charliexp/radmatrix/firmware/src/leds.cpp

#include <Arduino.h>
#include "hardware/gpio.h"
#include "pico/multicore.h"
#include "hardware/pio.h"

#include "leds.h"
#include "leds.pio.h"

PIO leds_pio = pio0;
uint pusher_sm = 255; // invalid
uint delay_sm = 255; // invalid
uint row_sm = 255; // invalid

// NOTE: RCLK, SRCLK capture on *rising* edge
inline void pulsePin(uint8_t pin) {
  gpio_put(pin, HIGH);
  asm volatile("nop \n nop \n nop");
  asm volatile("nop \n nop \n nop");
  asm volatile("nop \n nop \n nop");
  gpio_put(pin, LOW);
}

void clearShiftReg(uint8_t srclk, uint8_t srclr) {
  gpio_put(srclr, LOW);
  pulsePin(srclk);
  gpio_put(srclr, HIGH);
}

inline void outputEnable(uint8_t pin, bool enable) {
  gpio_put(pin, !enable);
}

// we have COLOR_BITS-bit color depth, so 2^COLOR_BITS levels of brightness
// we go from phase 0 to phase (COLOR_BITS-1)
uint8_t brightnessPhase = 0;
uint8_t ditheringPhase = 0;

#if DEBUG_FRAMEBUFFER
uint8_t framebuffer[ROW_COUNT * COL_COUNT] = {0};
#endif

// Framebuffer encoded for fast PIO pixel pushing
// There's one buffer for each of pixel's bit indices (aka brightness phases),
// Then for each row (laid out bottom to top), we have:
// - one 32-bit word per horizontal (column) module:
//     20 pixels = 24 shift register stages (4 placeholders), 7 unused bits,
//     1 bit to indicate end of row
// - one word for selecting (shifting) a row:
//     1 bit (LSB) to indicate start of frame (1) or not (0)
//     remaining bits to indicate a number of shift register pulses
//     (again, 24 shift register stages per 20 rows, so there are placeholders)
uint32_t ledBuffer[COLOR_BITS][ROW_COUNT * (COL_MODULES + 1)] = {0};
bool ledBufferReady = false;

void leds_set_framebuffer(uint8_t *buffer) {
  // TODO: Use a separate buffer, then copy to ledsBuffer to avoid tearing
  #define UNUSED_BITS 8 - COLOR_BITS
  for (int bi = 0; bi < COLOR_BITS; bi++) {
    uint8_t bitPosition = 1 << (bi + UNUSED_BITS);

    for (int yModule = 0; yModule < ROW_MODULES; yModule++) {
      for (int moduleY = 0; moduleY < 20; moduleY++) {
        auto y = yModule * 20 + moduleY;

        auto bufferYOffset = (ROW_COUNT - 1 - y) * COL_COUNT;
        auto outputYOffset = y * (COL_MODULES + 1);

        // set data for a given row
        for (int xModule = 0; xModule < COL_MODULES; xModule++) {
          auto bufferXOffset = bufferYOffset + xModule * 20;
          uint32_t sample = 0;

          for (int x = 0; x < 20; x++) {
            // insert placeholders for unused stages
            // (before pixels 0, 6, 13)
            if (x == 0 || x == 6 || x == 13) {
              sample >>= 1;
            }
            uint8_t px = buffer[bufferXOffset + x];
            bool bit = px & bitPosition;
            sample = (sample >> 1) | (bit ? 0x80000000 : 0);
          }
          // insert placeholder for unused last stage (after pixel 19)
          sample >>=1;
          // shift to LSB position
          sample >>=8;
          // MSB=1 indicates end of row
          if (xModule == COL_MODULES - 1) {
            sample |= 0x80000000;
          }

          ledBuffer[bi][outputYOffset + xModule] = sample;
        }

        // set row shifting data
        bool firstRow = y == 0;
        uint32_t extraPulses = 0;

        if (moduleY == 0) {
          extraPulses++;
        }

        if (moduleY == 7 || moduleY == 14 || (moduleY == 0 && yModule != 0)) {
          extraPulses++;
        }

        uint32_t rowData = firstRow | (extraPulses << 1);
        ledBuffer[bi][outputYOffset + COL_MODULES] = rowData;
      }
    }
  }
  ledBufferReady = true;

  #if DEBUG_FRAMEBUFFER
  // copy to framebuffer
  // TODO: mutex? double buffer? or something...
  memcpy(framebuffer, buffer, ROW_COUNT * COL_COUNT);
  #endif
}

void leds_init() {
  #if DEBUG_FRAMEBUFFER
  memset(framebuffer, 0, sizeof(framebuffer));
  #endif

  // disable output
  outputEnable(COL_OE, false);
  outputEnable(ROW_OE, false);

  // set up col pins
  pinMode(COL_SER, OUTPUT);
  pinMode(COL_OE, OUTPUT);
  outputEnable(ROW_OE, false);
  pinMode(COL_RCLK, OUTPUT);
  pinMode(COL_SRCLK, OUTPUT);
  pinMode(COL_SRCLR, OUTPUT);

  // set up row pins
  pinMode(ROW_SER, OUTPUT);
  pinMode(ROW_OE, OUTPUT);
  outputEnable(ROW_OE, false);
  pinMode(ROW_RCLK, OUTPUT);
  pinMode(ROW_SRCLK, OUTPUT);
  pinMode(ROW_SRCLR, OUTPUT);

  // set pin inversion
  #if COL_OE_INVERTED
  gpio_set_outover(COL_OE, GPIO_OVERRIDE_INVERT);
  #endif
  #if COL_SRCLR_INVERTED
  gpio_set_outover(COL_SRCLR, GPIO_OVERRIDE_INVERT);
  #endif

  // clear output
  clearShiftReg(COL_SRCLK, COL_SRCLR);
  clearShiftReg(ROW_SRCLK, ROW_SRCLR);

  pulsePin(COL_RCLK);
  pulsePin(ROW_RCLK);

  outputEnable(COL_OE, true); // this is fine, because we control OE via rows only
}

void leds_disable() {
  outputEnable(ROW_OE, false);
}

void main2() {
  // where we're going, we don't need no interrupts
  noInterrupts();
  while (true) {
    leds_render();
  }
}

void leds_initPIO();

void leds_initRenderer() {
  leds_initPIO();
  multicore_reset_core1();
  multicore_launch_core1(main2);
}

void leds_nextPhase() {
  brightnessPhase++;

  if (brightnessPhase == COLOR_BITS) {
    brightnessPhase = 0;
    ditheringPhase = (ditheringPhase + 1) % DITHERING_PHASES;
  }

  while (ditheringPhase >= brightnessPhaseDithering[brightnessPhase]) {
    brightnessPhase++;
  }
}

uint32_t *currentBuffer = nullptr;
uint32_t currentDelayData;
uint8_t currentY = 0;
uint8_t currentX = 0;

void leds_startFrame() {
  // next brightness phase
  leds_nextPhase();

  currentBuffer = ledBuffer[brightnessPhase];
  currentDelayData = brightnessPhaseDelays[brightnessPhase];
}

void leds_endRow() {
  // NOTE: pusher_sm is always the bottleneck, so we don't need to check for full TX FIFO here
  // set row selection data
  auto rowSelData = *currentBuffer++;
  assert(!pio_sm_is_tx_fifo_full(leds_pio, row_sm));
  pio_sm_put(leds_pio, row_sm, rowSelData);

  // set delay data
  assert(!pio_sm_is_tx_fifo_full(leds_pio, delay_sm));
  pio_sm_put(leds_pio, delay_sm, currentDelayData);

  // end of row
  currentX = 0;
  currentY++;

  // end of frame?
  if (currentY == ROW_COUNT) {
    currentY = 0;
    leds_startFrame();
  }
}

void leds_renderStep() {
  if (!ledBufferReady) {
    return;
  }

  // send row data
  auto pxValues = *currentBuffer++;
  assert(!pio_sm_is_tx_fifo_full(leds_pio, pusher_sm));
  pio_sm_put(leds_pio, pusher_sm, pxValues);

  // end of row
  currentX++;
  if (currentX == COL_MODULES) {
    leds_endRow();
  }
}

void leds_render() {
  // The correct data to push onto PIO has been precomputed by leds_set_framebuffer
  // So we only need to move the buffer onto PIO TX FIFOs to keep them full
  // TODO: Rewrite this to be interrupt-based. Should be relatively easy to always keep PIO
  // full via interrupts and free up most of the core's time to other tasks

  // start first frame
  leds_startFrame();

  while (true) {
    while (pio_sm_is_tx_fifo_full(leds_pio, pusher_sm)) {
      // busy wait
    }

    leds_renderStep();
  }
}

void leds_initPusher() {
  PIO pio = leds_pio;
  uint sm = pio_claim_unused_sm(pio, true);
  pusher_sm = sm;

  uint offset = pio_add_program(pio, &leds_px_pusher_program);

  pio_sm_config config = leds_px_pusher_program_get_default_config(offset);
  sm_config_set_clkdiv_int_frac(&config, LEDS_PIO_CLKDIV, 0);

  // Shift OSR to the right, autopull
  sm_config_set_out_shift(&config, true, true, 32);

  // Use FIFO join to create a longer TX FIFO
  // NOTE: This is not needed for the other SMs, as the px pusher will always be the bottleneck
  sm_config_set_fifo_join(&config, PIO_FIFO_JOIN_TX);

  // Set OUT (data) pin, connect to pad, set as output
  sm_config_set_out_pins(&config, COL_SER, 1);
  pio_gpio_init(pio, COL_SER);
  pio_sm_set_consecutive_pindirs(pio, sm, COL_SER, 1, true);
  #if COL_SER_INVERTED
  gpio_set_outover(COL_SER, GPIO_OVERRIDE_INVERT);
  #endif

  // Set sideset (SRCLK) pin, connect to pad, set as output
  sm_config_set_sideset_pins(&config, COL_SRCLK);
  pio_gpio_init(pio, COL_SRCLK);
  pio_sm_set_consecutive_pindirs(pio, sm, COL_SRCLK, 1, true);
  #if COL_SRCLK_INVERTED
  gpio_set_outover(COL_SRCLK, GPIO_OVERRIDE_INVERT);
  #endif
  // gpio_set_drive_strength(COL_SRCLK, GPIO_DRIVE_STRENGTH_12MA);

  // Set SET (RCLK) pin, connect to pad, set as output
  sm_config_set_set_pins(&config, COL_RCLK, 1);
  pio_gpio_init(pio, COL_RCLK);
  pio_sm_set_consecutive_pindirs(pio, sm, COL_RCLK, 1, true);
  #if COL_RCLK_INVERTED
  gpio_set_outover(COL_RCLK, GPIO_OVERRIDE_INVERT);
  #endif
  // gpio_set_drive_strength(COL_RCLK, GPIO_DRIVE_STRENGTH_12MA);

  // Load our configuration, and jump to the start of the program
  pio_sm_init(pio, sm, offset, &config);
  pio_sm_set_enabled(pio, sm, true);
}

void leds_initRowSelector() {
  PIO pio = leds_pio;
  uint sm = pio_claim_unused_sm(pio, true);
  row_sm = sm;

  uint offset = pio_add_program(pio, &leds_row_selector_program);

  pio_sm_config config = leds_row_selector_program_get_default_config(offset);
  sm_config_set_clkdiv_int_frac(&config, LEDS_PIO_CLKDIV, 0);

  // Shift OSR to the right, autopull
  sm_config_set_out_shift(&config, true, true, 32);

  // Set OUT/MOV (data) pin, connect to pad, set as output
  sm_config_set_out_pins(&config, ROW_SER, 1);
  pio_gpio_init(pio, ROW_SER);
  pio_sm_set_consecutive_pindirs(pio, sm, ROW_SER, 1, true);

  // Set sideset (SRCLK) pin, connect to pad, set as output
  sm_config_set_sideset_pins(&config, ROW_SRCLK);
  pio_gpio_init(pio, ROW_SRCLK);
  pio_sm_set_consecutive_pindirs(pio, sm, ROW_SRCLK, 1, true);

  // Set SET (RCLK) pin, connect to pad, set as output
  sm_config_set_set_pins(&config, ROW_RCLK, 1);
  pio_gpio_init(pio, ROW_RCLK);
  pio_sm_set_consecutive_pindirs(pio, sm, ROW_RCLK, 1, true);

  // Load our configuration, and jump to the start of the program
  pio_sm_init(pio, sm, offset, &config);
  pio_sm_set_enabled(pio, sm, true);
}

void leds_initDelay() {
  PIO pio = leds_pio;
  uint sm = pio_claim_unused_sm(pio, true);
  delay_sm = sm;

  uint offset = pio_add_program(pio, &leds_delay_program);

  pio_sm_config config = leds_delay_program_get_default_config(offset);
  sm_config_set_clkdiv_int_frac(&config, LEDS_PIO_CLKDIV, 0);

  // Shift OSR to the right, autopull
  sm_config_set_out_shift(&config, true, true, 32);

  // Set sideset (OE) pin, connect to pad, set as output
  sm_config_set_sideset_pins(&config, ROW_OE);
  pio_gpio_init(pio, ROW_OE);
  pio_sm_set_consecutive_pindirs(pio, sm, ROW_OE, 1, true);

  // Load our configuration, and jump to the start of the program
  pio_sm_init(pio, sm, offset, &config);
  pio_sm_set_enabled(pio, sm, true);
}

void leds_initPIO() {
  leds_initPusher();
  leds_initDelay();
  leds_initRowSelector();
}
