charliexp/radmatrix/firmware/src/audio.cpp

#include <Arduino.h>
#include "hardware/irq.h"  // interrupts
#include "hardware/pwm.h"  // pwm
#include "hardware/sync.h" // wait for interrupt
#include "hardware/gpio.h"
#include "audio.h"

// Adapted from https://github.com/rgrosset/pico-pwm-audio

#define MAX_PWM_POS (BUFFER_LEN << 3)

uint8_t wav_buffer_0[BUFFER_LEN] = {0};
uint8_t wav_buffer_1[BUFFER_LEN] = {0};
bool wav_buffer1_active = false;
volatile bool next_buffer_requested = false; // horrible, use some interrupt-based solution or at least locks or whatever
uint32_t pwm_position = 0;

/*
 * PWM Interrupt Handler which outputs PWM level and advances the
 * current sample.
 *
 * We repeat the same value for 8 cycles this means sample rate etc
 * adjust by factor of 8   (this is what bitshifting <<3 is doing)
 *
 */
void pwm_interrupt_handler() {
    pwm_clear_irq(pwm_gpio_to_slice_num(AUDIO_PIN));
    if (pwm_position < MAX_PWM_POS - 1) {
        auto wav_buffer = wav_buffer1_active ? wav_buffer_1 : wav_buffer_0;
        // set pwm level
        // allow the pwm value to repeat for 8 cycles this is >>3
        pwm_set_gpio_level(AUDIO_PIN, wav_buffer[pwm_position>>3]);
        pwm_position++;
    } else {
        // reset to start, flip to other buffer
        pwm_position = 0;
        next_buffer_requested = true;
        wav_buffer1_active = !wav_buffer1_active;
    }
}

// 11 KHz is fine for speech. Phone lines generally sample at 8 KHz
#define AUDIO_WRAP 256.0f
#define AUDIO_CLK_DIV (CPU_CLOCK_HZ / AUDIO_WRAP / 8.0f / AUDIO_RATE)

void init_audio() {
    gpio_set_function(AUDIO_PIN, GPIO_FUNC_PWM);

    int audio_pin_slice = pwm_gpio_to_slice_num(AUDIO_PIN);

    // Setup PWM interrupt to fire when PWM cycle is complete
    pwm_clear_irq(audio_pin_slice);
    pwm_set_irq_enabled(audio_pin_slice, true);

    // set the handle function above
    irq_set_exclusive_handler(PWM_IRQ_WRAP, pwm_interrupt_handler);
    // irq_set_enabled(PWM_IRQ_WRAP, true);

    // Setup PWM for audio output
    pwm_config config = pwm_get_default_config();

    pwm_config_set_clkdiv(&config, AUDIO_CLK_DIV);
    pwm_config_set_wrap(&config, AUDIO_WRAP);
    pwm_init(audio_pin_slice, /*0,*/ &config, true);

    pwm_set_gpio_level(AUDIO_PIN, 0);
}

void audio_stop() {
    Serial.println("audio_stop");
    irq_set_enabled(PWM_IRQ_WRAP, false);
    pwm_set_gpio_level(AUDIO_PIN, 0);
}

void audio_start() {
    Serial.println("audio_start");
    audio_stop();
    pwm_position = 0;
    wav_buffer1_active = false;
    irq_set_enabled(PWM_IRQ_WRAP, true);
}
